SgtLexington/Buzzer-System/Pictures/20180710_123230.jpg

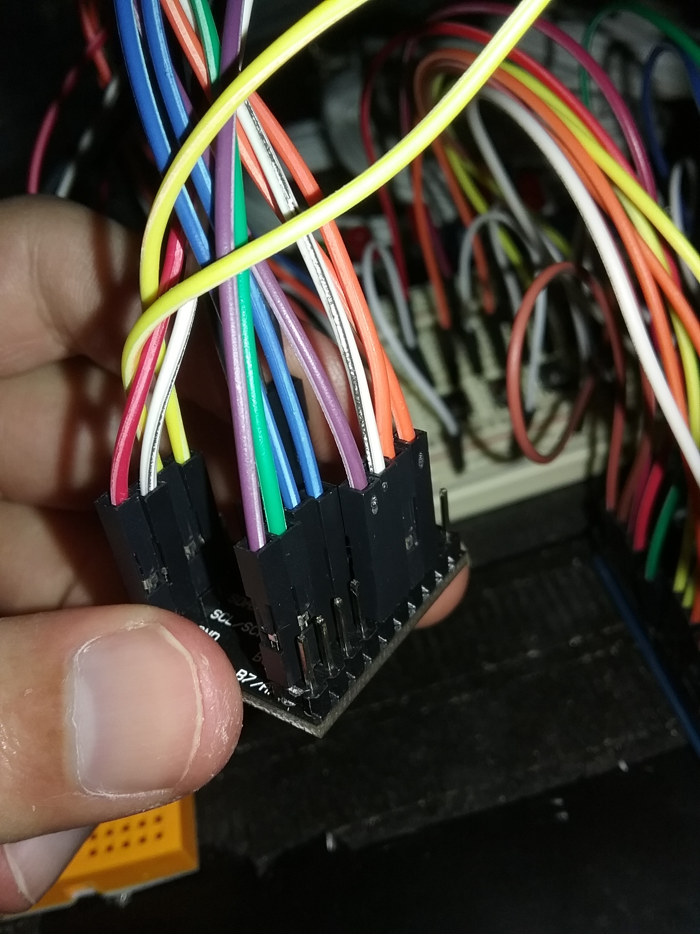
Pictures/20180710_123230.jpg
