SgtLexington/Buzzer-System/Pictures/20180710_123253.jpg

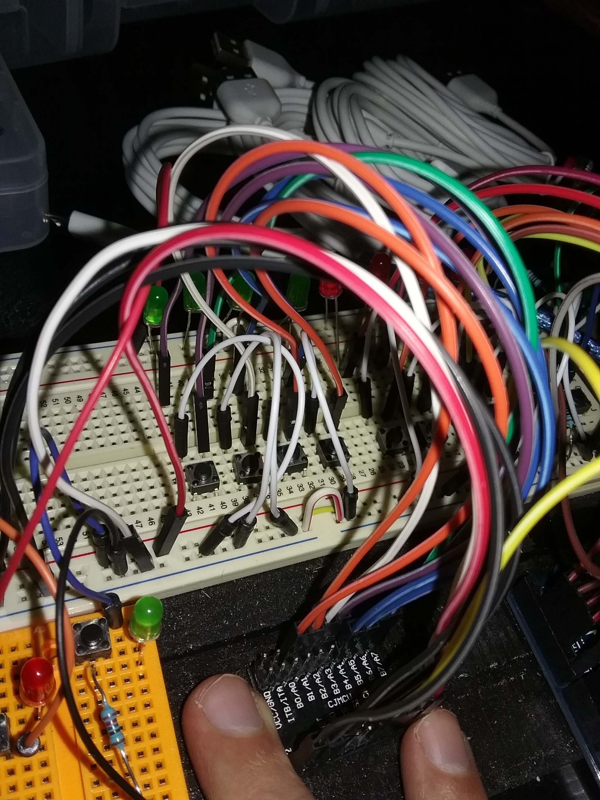
Pictures/20180710_123253.jpg
