SgtLexington/Buzzer-System/Pictures/20180710_123303.jpg

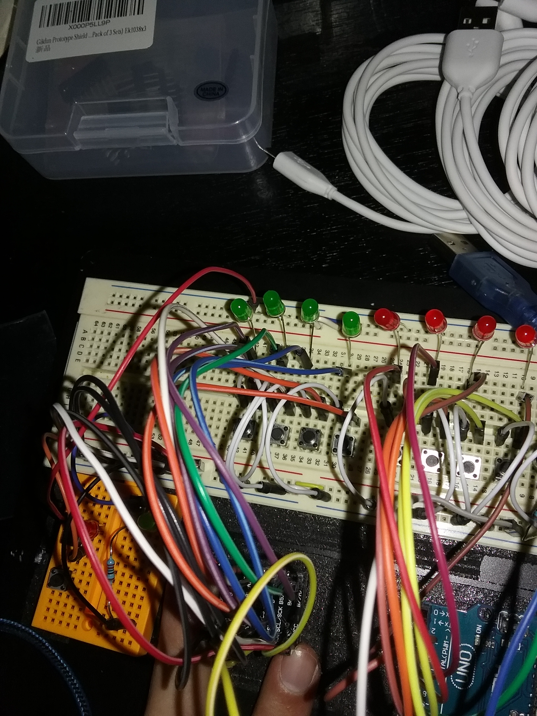
Pictures/20180710_123303.jpg
