SgtLexington/Buzzer-System/Pictures/20180727_124211.jpg

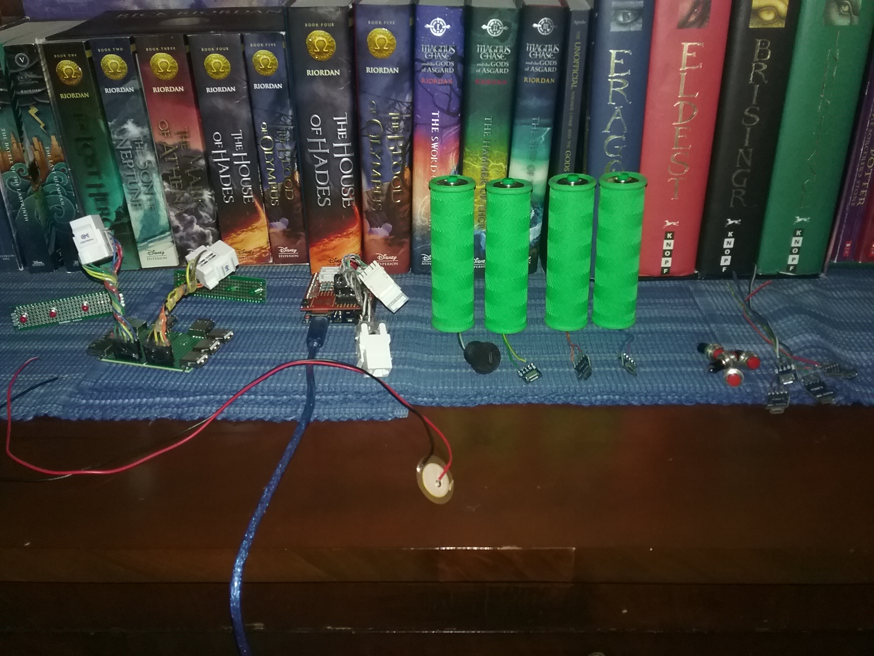
Pictures/20180727_124211.jpg
