SgtLexington/Buzzer-System/Pictures/20181017_192755.jpg

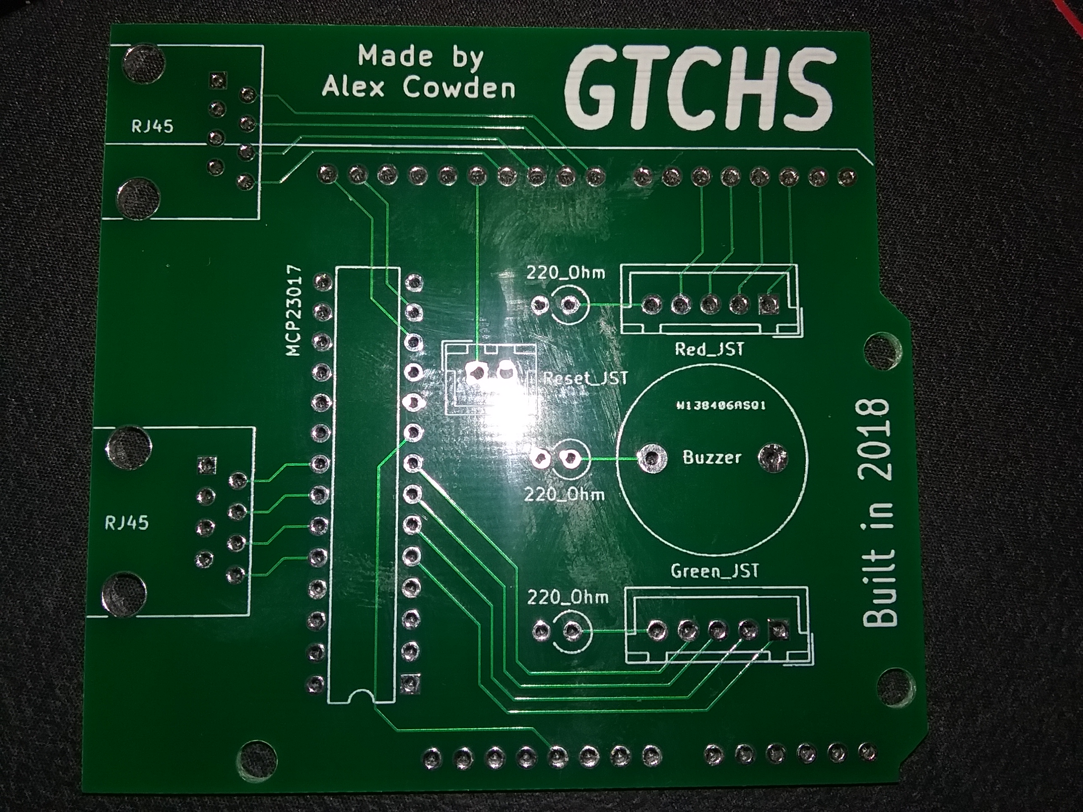
Pictures/20181017_192755.jpg
