SgtLexington/Buzzer-System/Pictures/20181017_192809.jpg

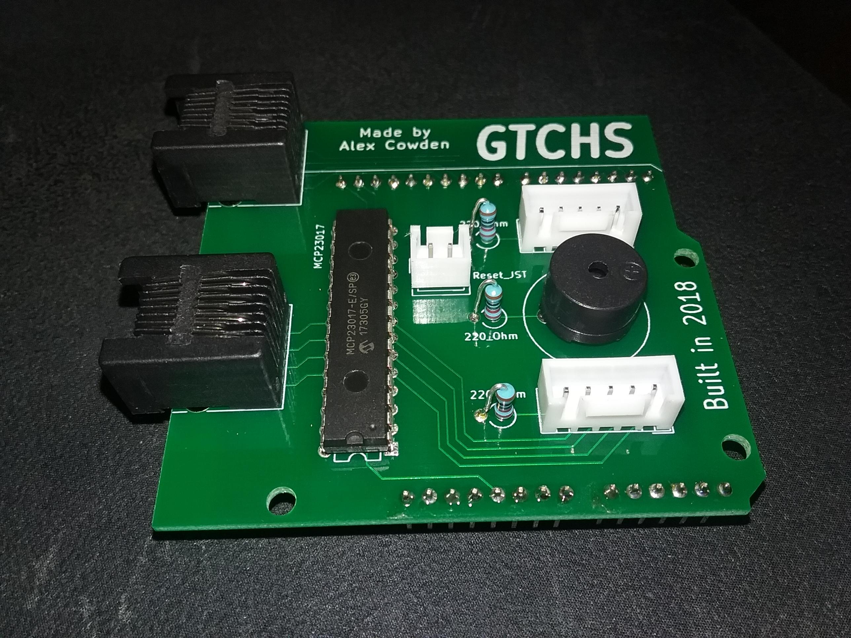
Pictures/20181017_192809.jpg
