SgtLexington/Buzzer-System/Pictures/20181203_163640.jpg

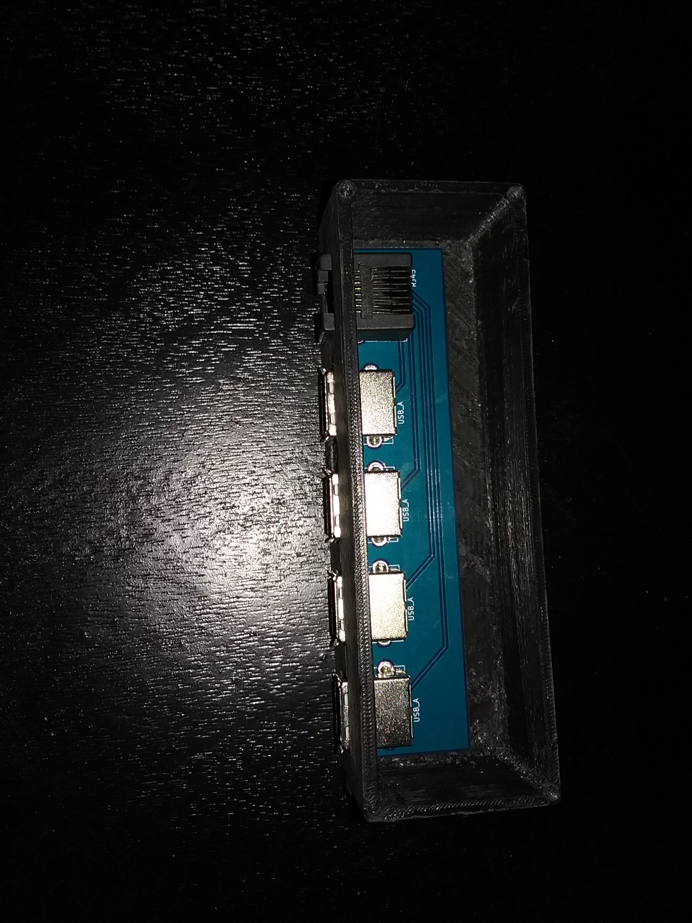
Pictures/20181203_163640.jpg
