SgtLexington/Buzzer-System/Pictures/20181203_170350.jpg

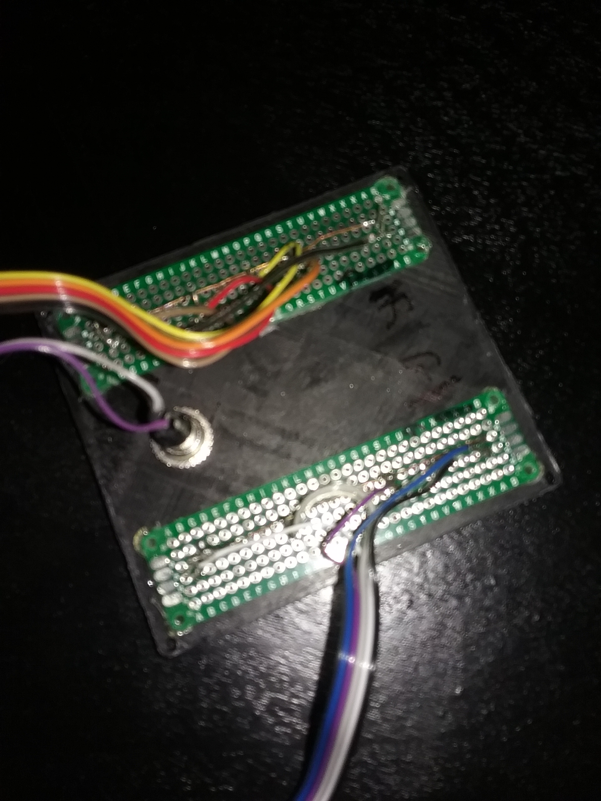
Pictures/20181203_170350.jpg
