SgtLexington/Buzzer-System/Pictures/20181203_171628.jpg

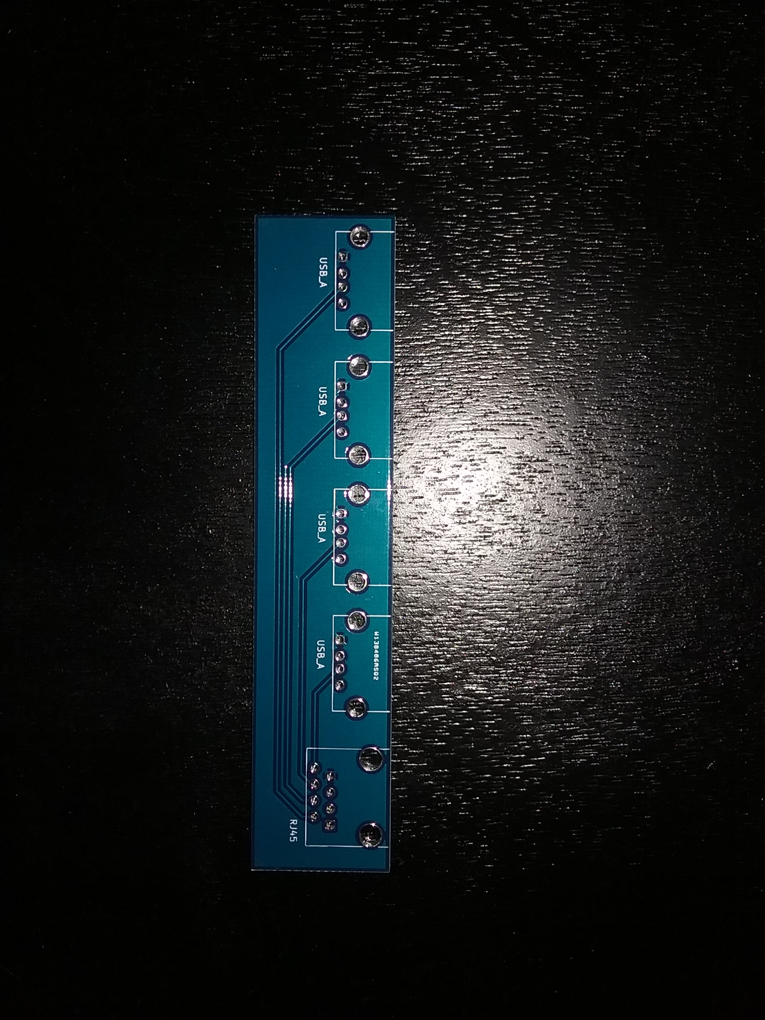
Pictures/20181203_171628.jpg
