SgtLexington/Buzzer-System/Pictures/20181203_171857.jpg

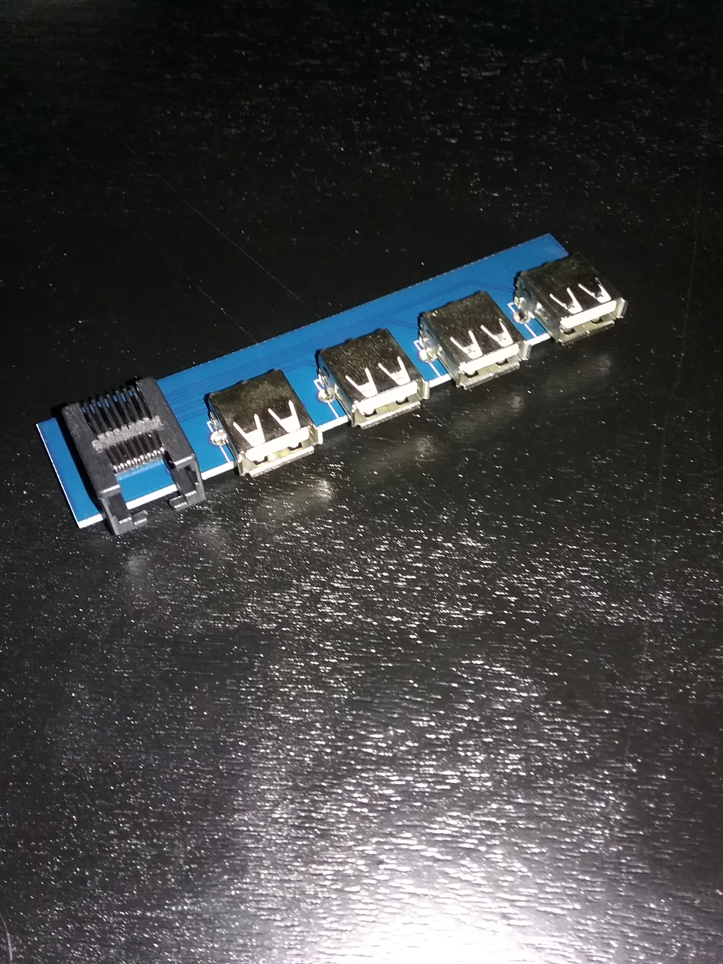
Pictures/20181203_171857.jpg
