SgtLexington/Buzzer-System/Pictures/20181203_172249.jpg

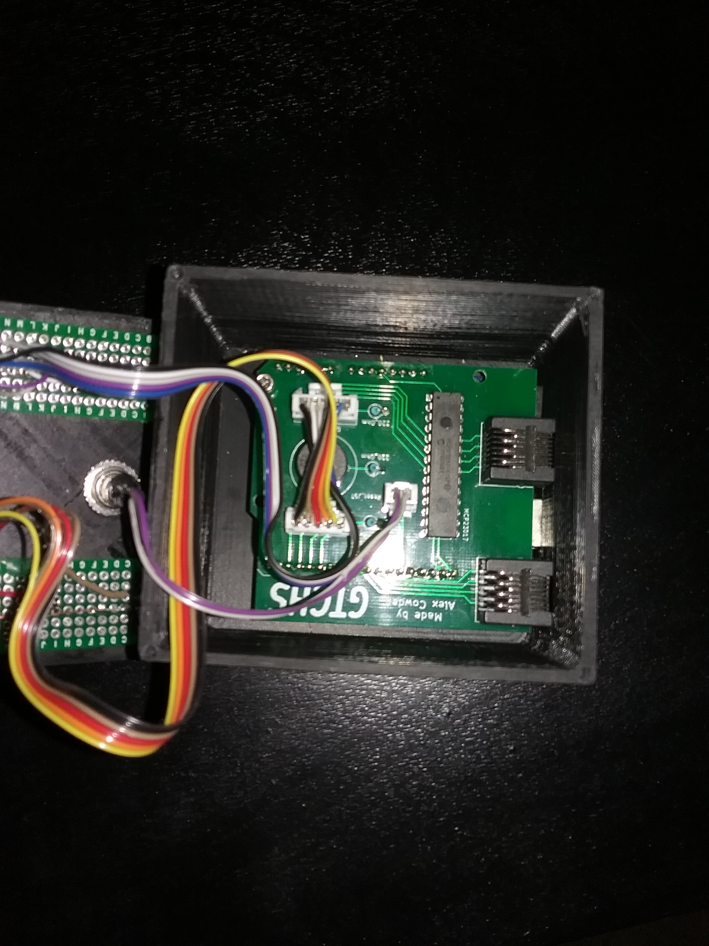
Pictures/20181203_172249.jpg
