SgtLexington/Buzzer-System/Pictures/20181203_172655.jpg

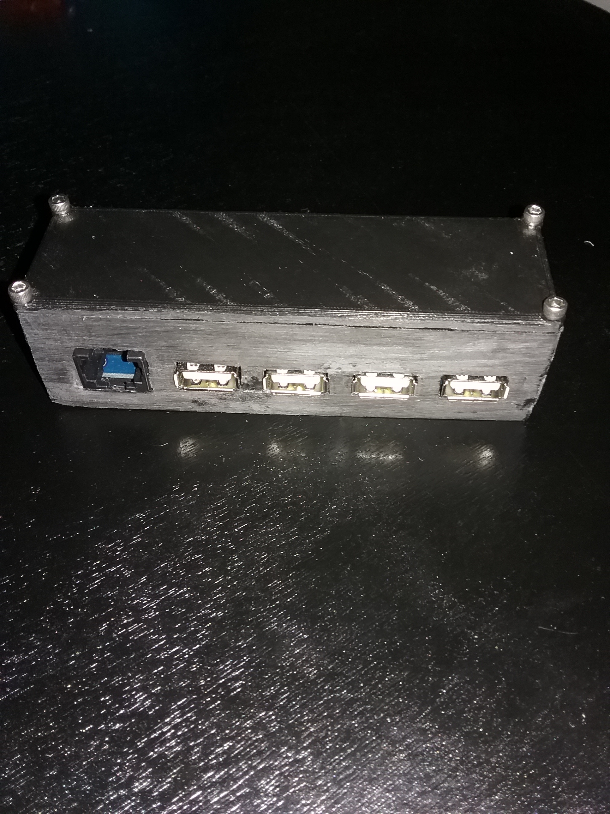
Pictures/20181203_172655.jpg
