SgtLexington/Buzzer-System/Pictures/20181203_172840.jpg

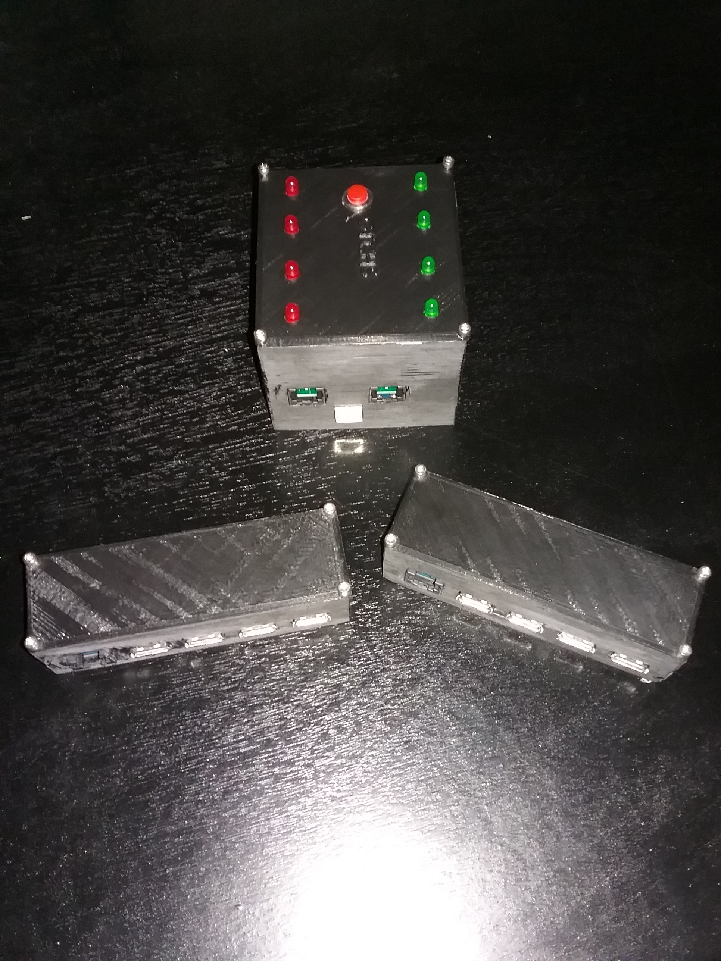
Pictures/20181203_172840.jpg
