SgtLexington/Buzzer-System/Pictures/20181208_133736.jpg

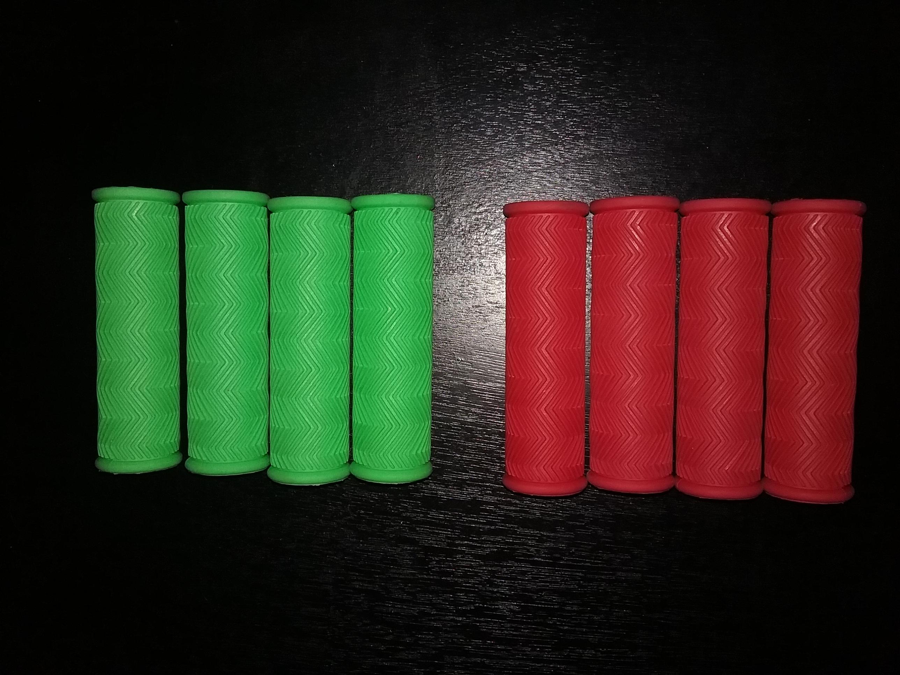
Pictures/20181208_133736.jpg
