SgtLexington/Buzzer-System/Pictures/20181208_135711.jpg

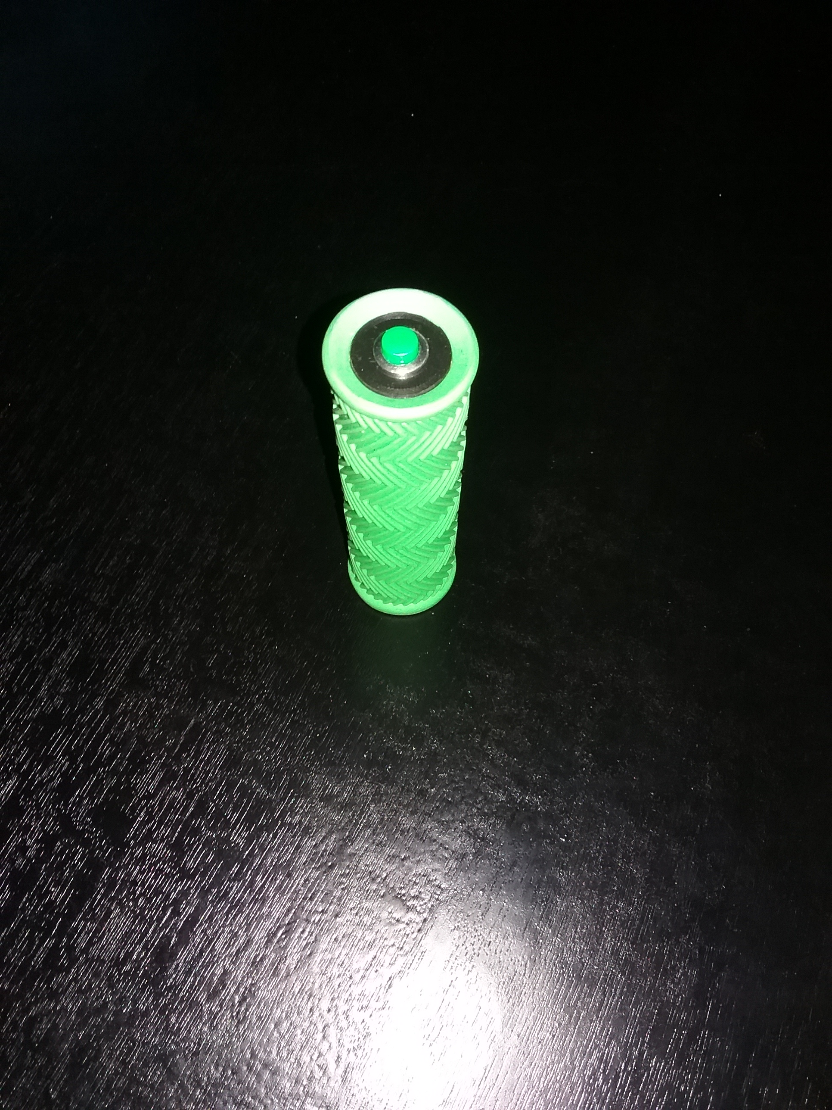
Pictures/20181208_135711.jpg
