SgtLexington/Buzzer-System/Pictures/20181208_135853.jpg

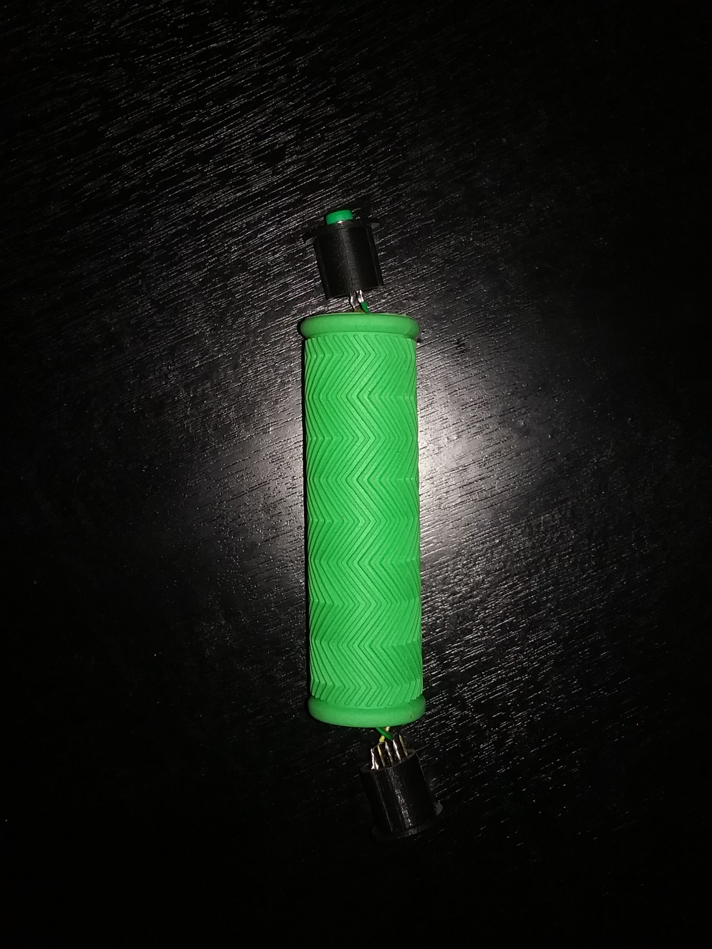
Pictures/20181208_135853.jpg
