SgtLexington/Buzzer-System/Pictures/20181208_141430.jpg

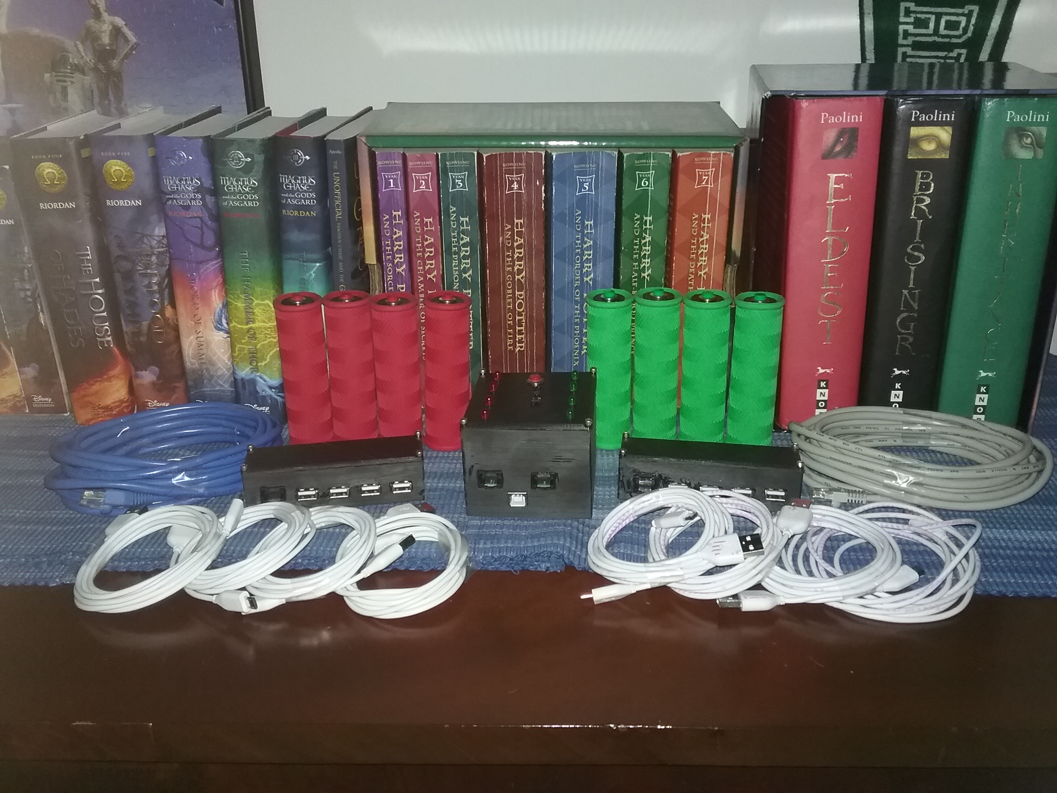
Pictures/20181208_141430.jpg
